HLammers/cybo-drummer/src/font.py

''' 6x8 Cybo-Drummer font for Cybo-Drummer - Humanize Those Drum Computers!
    https://github.com/HLammers/cybo-drummer
    Copyright (c) 2025 Harm Lammers

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
    You should have received a copy of the GNU General Public License along with this program. If not, see https://www.gnu.org/licenses/.'''

_MIN_CH  = const(32)

_g = (
b'\x00\x00\x00\x00\x00\x00\x00\x00', # 032: space
b'\x20\x20\x20\x20\x20\x00\x20\x00', # 033: !
b'\xD8\x48\x90\x00\x00\x00\x00\x00', # 034: "
b'\x00\x50\xF8\x50\x50\xF8\x50\x00', # 035: #
b'\x20\x70\x80\x70\x08\x88\x70\x20', # 036: $
b'\x00\xD0\xD0\x20\x20\x58\x58\x00', # 037: %
b'\x20\x50\x50\x60\xA8\x90\x68\x00', # 038: &
b'\x30\x10\x20\x00\x00\x00\x00\x00', # 039: '
b'\x10\x20\x20\x20\x20\x20\x20\x10', # 040: (
b'\x20\x10\x10\x10\x10\x10\x10\x20', # 041: )
b'\x00\x20\xA8\x70\x70\xA8\x20\x00', # 042: *
b'\x00\x20\x20\xF8\x20\x20\x00\x00', # 043: +
b'\x00\x00\x00\x00\x00\x30\x10\x20', # 044: ,
b'\x00\x00\x00\xF8\x00\x00\x00\x00', # 045: -
b'\x00\x00\x00\x00\x00\x30\x30\x00', # 046: .
b'\x00\x10\x10\x20\x20\x40\x40\x00', # 047: /
b'\x70\x88\x88\xA8\x88\x88\x70\x00', # 048: 0
b'\x60\x10\x10\x10\x10\x10\x10\x00', # 049: 1
b'\x70\x88\x08\x08\x70\x80\xF8\x00', # 050: 2
b'\x70\x88\x08\x30\x08\x88\x70\x00', # 051: 3
b'\x88\x88\x88\x78\x08\x08\x08\x00', # 052: 4
b'\xF8\x80\xF0\x08\x08\x88\x70\x00', # 053: 5
b'\x70\x88\x80\xF0\x88\x88\x70\x00', # 054: 6
b'\xF0\x08\x08\x10\x20\x40\x80\x00', # 055: 7
b'\x70\x88\x88\x70\x88\x88\x70\x00', # 056: 8
b'\x70\x88\x88\x78\x08\x88\x70\x00', # 057: 9
b'\x00\x30\x30\x00\x00\x30\x30\x00', # 058: :
b'\x00\x30\x30\x00\x00\x30\x10\x20', # 059: ;
b'\x08\x10\x20\x40\x20\x10\x08\x00', # 060: <
b'\x00\x00\xF8\x00\xF8\x00\x00\x00', # 061: =
b'\x40\x20\x10\x08\x10\x20\x40\x00', # 062: >
b'\x70\x88\x08\x10\x20\x00\x20\x00', # 063: ?
b'\x70\x88\x98\xA8\xA8\x98\x80\x70', # 064: @
b'\x70\x88\x88\x88\xF8\x88\x88\x00', # 065: A
b'\xF0\x88\x88\xF0\x88\x88\xF0\x00', # 066: B
b'\x70\x88\x80\x80\x80\x88\x70\x00', # 067: C
b'\xF0\x88\x88\x88\x88\x88\xF0\x00', # 068: D
b'\x78\x80\x80\xE0\x80\x80\x78\x00', # 069: E
b'\x78\x80\x80\x80\xE0\x80\x80\x00', # 070: F
b'\x70\x88\x80\x80\x98\x88\x70\x00', # 071: G
b'\x88\x88\x88\xF8\x88\x88\x88\x00', # 072: H
b'\x20\x20\x20\x20\x20\x20\x20\x00', # 073: I
b'\x08\x08\x08\x08\x08\x88\x70\x00', # 074: J
b'\x84\x88\x90\xA0\xD0\x88\x84\x00', # 075: K
b'\x80\x80\x80\x80\x80\x80\xF8\x00', # 076: L
b'\x50\xA0\xA8\x88\x88\x88\x88\x00', # 077: M
b'\x70\x88\x88\x88\x88\x88\x88\x00', # 078: N
b'\x70\x88\x88\x88\x88\x88\x70\x00', # 079: O
b'\x70\x88\x88\x88\xF0\x80\x80\x00', # 080: P
b'\x70\x88\x88\x88\x88\x88\x70\x18', # 081: Q
b'\xF0\x88\x88\x88\xF0\x90\x88\x00', # 082: R
b'\x70\x88\x80\x70\x08\x88\x70\x00', # 083: S
b'\xF8\x20\x20\x20\x20\x20\x20\x00', # 084: T
b'\x88\x88\x88\x88\x88\x88\x70\x00', # 085: U
b'\x88\x88\x88\x88\x88\x50\x20\x00', # 086: V
b'\x88\x88\x88\x88\xA8\xA8\x50\x00', # 087: W
b'\x88\x88\x50\x20\x50\x88\x88\x00', # 088: X
b'\x88\x88\x88\x78\x08\x88\x70\x00', # 089: Y
b'\xF8\x08\x08\x70\x80\x80\xF8\x00', # 090: Z
b'\x30\x20\x20\x20\x20\x20\x20\x30', # 091: [
b'\x00\x40\x40\x20\x20\x10\x10\x00', # 092: \
b'\x30\x10\x10\x10\x10\x10\x10\x30', # 093: ]
b'\x20\x50\x00\x00\x00\x00\x00\x00', # 094: ^
b'\x00\x00\x00\x00\x00\x00\xF8\x00', # 095: _
b'\x30\x20\x10\x00\x00\x00\x00\x00', # 096: `
b'\x00\x70\x08\x78\x88\x88\x74\x00', # 097: a
b'\x80\x80\xF0\x88\x88\x88\x70\x00', # 098: b
b'\x00\x70\x88\x80\x80\x88\x70\x00', # 099: c
b'\x08\x08\x78\x88\x88\x88\x74\x00', # 100: d
b'\x00\x70\x88\x88\xB0\x80\x78\x00', # 101: e
b'\x20\x50\x40\x40\x60\x40\x40\x00', # 102: f
b'\x00\x70\x88\x88\x88\x78\x08\x30', # 103: g
b'\x80\x80\xF0\x88\x88\x88\x88\x00', # 104: h
b'\x20\x00\x20\x20\x20\x20\x10\x00', # 105: i
b'\x10\x00\x10\x10\x10\x10\x10\x20', # 106: j
b'\x80\x80\x88\x90\xA0\xD0\x88\x00', # 107: k
b'\x20\x20\x20\x20\x20\x20\x10\x00', # 108: l
b'\x00\x50\xA8\xA8\xA8\x88\x88\x00', # 109: m
b'\x00\x70\x88\x88\x88\x88\x88\x00', # 110: n
b'\x00\x70\x88\x88\x88\x88\x70\x00', # 111: o
b'\x00\x70\x88\x88\x88\xF0\x80\x80', # 112: p
b'\x00\x70\x88\x88\x88\x78\x08\x08', # 113: q
b'\x00\x70\x88\x80\x80\x80\x80\x00', # 114: r
b'\x00\x70\x80\x70\x08\x88\x70\x00', # 115: s
b'\x40\x40\x60\x40\x40\x50\x20\x00', # 116: t
b'\x00\x88\x88\x88\x88\x88\x74\x00', # 117: u
b'\x00\x88\x88\x88\x88\x50\x20\x00', # 118: v
b'\x00\x88\x88\xA8\xA8\xA8\x50\x00', # 119: w
b'\x00\x88\x50\x20\x20\x50\x88\x00', # 120: x
b'\x00\x88\x88\x88\x88\x78\x08\x30', # 121: y
b'\x00\xF8\x08\x08\x70\x80\xF8\x00', # 122: z
b'\x10\x20\x20\x40\x40\x20\x20\x10', # 123: {
b'\x20\x20\x20\x20\x20\x20\x20\x20', # 124: |
b'\x40\x20\x20\x10\x10\x20\x20\x40', # 125: }
b'\x28\x50\x00\x00\x00\x00\x00\x00', # 126: ~
b'\x1C\x20\x20\x20\x20\x20\x20\x1C', # 127: unchecked (left)
b'\xE0\x10\x10\x10\x10\x10\x10\xE0', # 128: unchecked (right)
b'\x1C\x20\x20\x20\x28\x24\x20\x1C', # 129: checked (left)
b'\xE0\x10\x30\x50\x90\x10\x10\xE0', # 130: checked (right)
b'\x00\x18\x3C\x18\x00\x3C\x00\x00', # 131: program (left)
b'\x00\x00\xF0\x00\xC0\xF0\xC0\x00', # 132: program (right)
b'\x34\x34\x00\x34\x34\x00\x34\x34', # 133: matrix (left)
b'\xB0\xB0\x00\xB0\xB0\x00\xB0\xB0', # 134: matrix (right)
b'\x1C\x00\x00\x3C\x3C\x00\x00\x1C', # 135: input (left)
b'\xE0\x10\x90\xD0\xD0\x90\x10\xE0', # 136: input (right)
b'\x1C\x20\x20\x2C\x2C\x20\x20\x1C', # 137: output (left)
b'\xE0\x00\x20\xF0\xF0\x20\x00\xE0', # 138: output (right)
b'\x00\x04\x04\x04\x0C\x1C\x38\x10', # 139: tools (left)
b'\xC0\x80\x90\xF0\xE0\x00\x00\x00', # 140: tools (right)
b'\x3C\x20\x20\x20\x20\x3C\x04\x1C', # 141: monitor (left)
b'\xF0\x10\x10\x10\x10\xF0\x80\xE0', # 142: monitor (right)
b'\x08\x0C\x3C\x18\x18\x3C\x0C\x08', # 143: settings (left)
b'\x40\xC0\xF0\x60\x60\xF0\xC0\x40', # 144: settings (right)
b'\x00\x00\x30\x78\x78\x30\x00\x00', # 145: centre
b'\x00\x78\xCC\x84\x84\xCC\x78\x00', # 146: rim/edge
b'\x00\x00\x30\x48\x48\x30\x00\x00', # 147: bow
b'\x00\x00\x00\x30\x30\x00\x00\x00', # 148: bell
b'\x00\x84\x48\x30\x30\x48\x84\x00', # 149: choke
b'\xC0\xD8\x04\x78\x7C\x7C\x3C\x3C', # 150: foot
b'\x00\x88\x94\x94\x9C\x94\xD4\x00', # 151: layer A
b'\x00\x98\x94\x98\x94\x94\xD8\x00', # 152: layer B
b'\x00\x88\x94\x90\x90\x94\xC8\x00', # 153: layer C
b'\x00\x98\x94\x94\x94\x94\xD8\x00', # 154: layer D
b'\x3C\x04\x04\x04\x04\x04\x04\x00', # 155: hard (left)
b'\x00\x00\x00\x00\x00\x00\xE0\x00', # 156: hard (right)
b'\x38\x04\x04\x04\x04\x04\x00\x00', # 157: smooth 1 (left)
b'\x00\x00\x00\x00\x00\x00\xE0\x00', # 158: smooth 1 (right)
b'\x30\x08\x04\x04\x04\x00\x00\x00', # 159: smooth 2 (left)
b'\x00\x00\x00\x00\x00\x80\x60\x00', # 160: smooth 2 (right)
b'\x20\x10\x08\x04\x00\x00\x00\x00', # 161: linear transient (left)
b'\x00\x00\x00\x00\x80\x40\x20\x00', # 162: linear transient (right)
b'\x00\x00\x00\x00\x00\x00\x3C\x00', # 163: negative 3 (left)
b'\x20\x20\x20\x20\x40\x80\x00\x00', # 164: negative 3 (right)
b'\x00\x00\x00\x00\x00\x0C\x30\x00', # 165: negative 2 (left)
b'\x20\x20\x40\x40\x80\x00\x00\x00', # 166: negative 2 (right)
b'\x00\x00\x00\x00\x04\x08\x30\x00', # 167: negative 1 (left)
b'\x20\x20\x40\x80\x00\x00\x00\x00', # 168: negative 1 (right)
b'\x00\x00\x00\x04\x08\x10\x20\x00', # 169: linear curve (left)
b'\x20\x40\x80\x00\x00\x00\x00\x00', # 170: linear curve (right)
b'\x20\x20\x10\x08\x04\x00\x00\x00', # 171: positive 1 (left)
b'\x00\x00\x00\x00\x00\x80\x60\x00', # 172: positive 1 (right)
b'\x20\x20\x10\x10\x08\x04\x00\x00', # 173: positive 2 (left)
b'\x00\x00\x00\x00\x00\x80\x60\x00', # 174: positive 2 (right)
b'\x20\x20\x20\x20\x10\x08\x04\x00', # 175: positive 3 (left)
b'\x20\x20\x70\x70\xF8\xF8\x00\x00', # 176: up
b'\x00\x00\xF8\xF8\x70\x70\x20\x20', # 177: down
b'\x24\x24\x24\x24\x24\x24\x24\x24', # 178: up right (right)
b'\x20\x70\x20\x20\x20\x20\x20\x20', # 179: up right (right)
b'\x00\x3C\x00\x00\x3C\x00\x00\x3C', # 180: right up (right)
b'\x20\xF0\x20\x00\xF0\x00\x00\xF0', # 181: right up (right)
)

def get_ch(n: int) -> memoryview:
    '''get reference to character data; called by Display.text_box'''
    return memoryview(_g[n - _MIN_CH])
